rizkarezap/Pangandaran-Project-Smart-Coconut-Plantation/Board/Pangandaran Board V1/PangandaranV_JST1.pdf

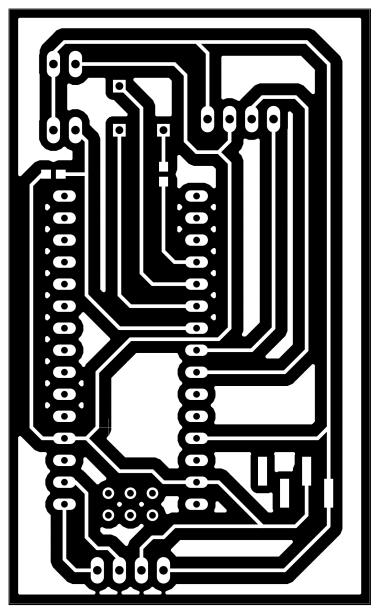
[picture p7: page 1]
