rizkarezap/Pangandaran-Project-Smart-Coconut-Plantation/Board/Pangandaran Board V3/PasurV3.pdf

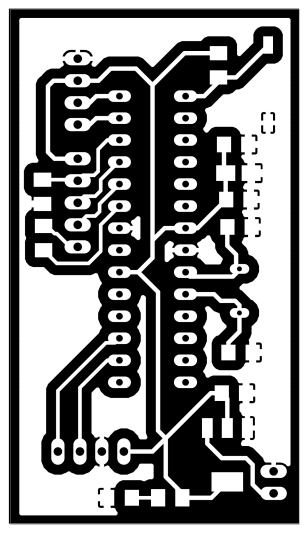
[picture p8: page 1]
